WilliTourt/ESP32-Desktop-Drumkit-v0-Prototype/Hardware_PCB/Schematic/Piezo WaveHandler.png

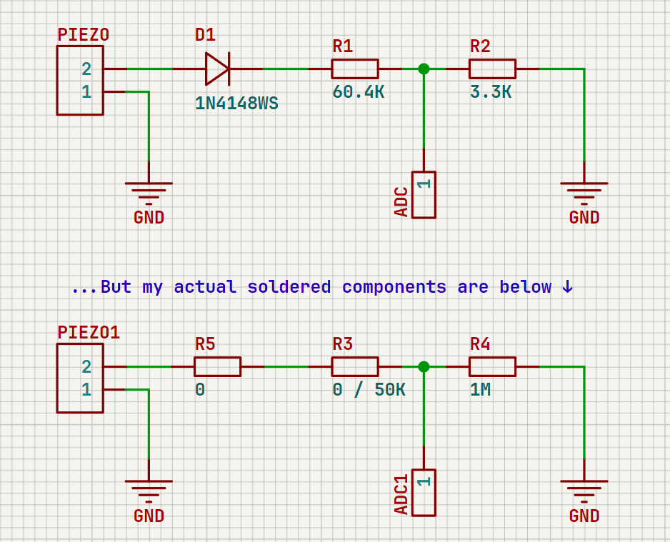
Hardware_PCB/Schematic/Piezo WaveHandler.png
