WilliTourt/ESP32-Desktop-Drumkit-v0-Prototype/Images of Drumkit/IMG_20250831_215929.jpg

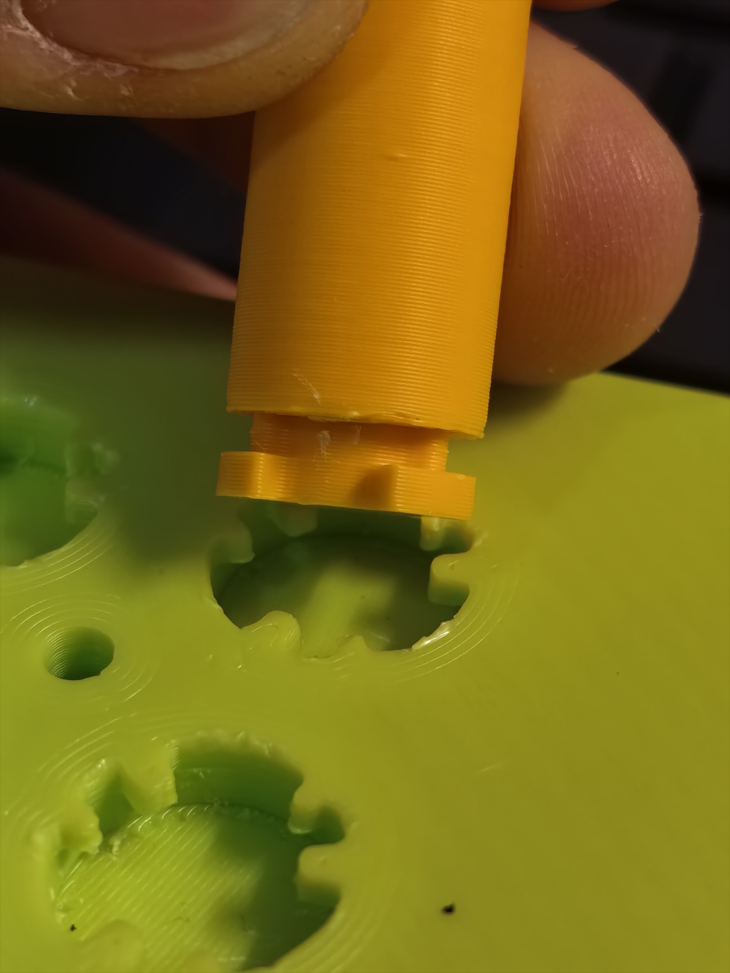
Images of Drumkit/IMG_20250831_215929.jpg
