WilliTourt/ESP32-Desktop-Drumkit-v0-Prototype/Images of Drumkit/IMG_20250901_182324.jpg

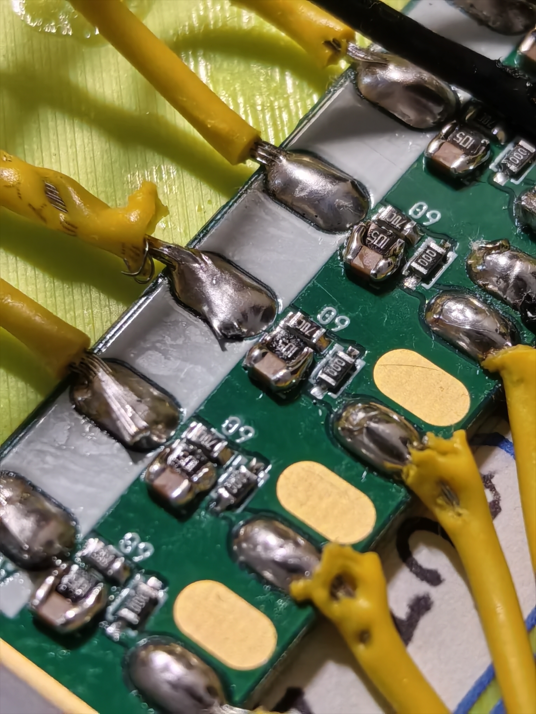
Images of Drumkit/IMG_20250901_182324.jpg
