WilliTourt/ESP32-Desktop-Drumkit-v0-Prototype/Images of Drumkit/IMG_20250902_012816.jpg

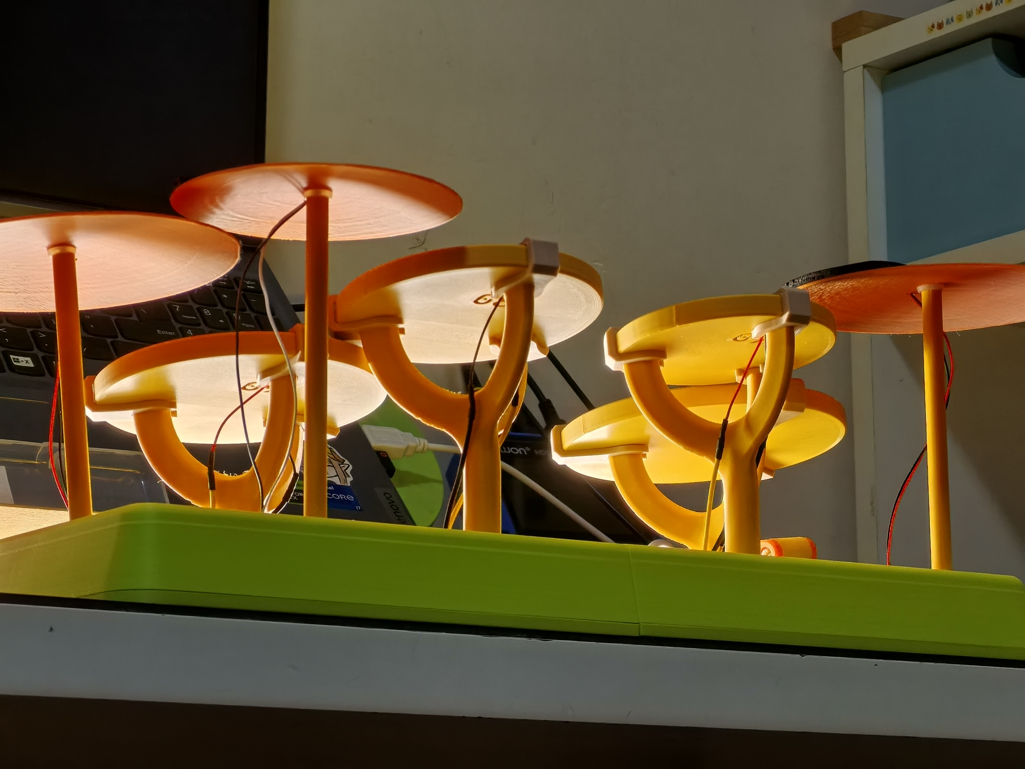
Images of Drumkit/IMG_20250902_012816.jpg
