WilliTourt/ESP32-Desktop-Drumkit-v0-Prototype/ESP32 Desktop Drumkit 3D Parts/STEP Files/Cymbal_9cm.STEP

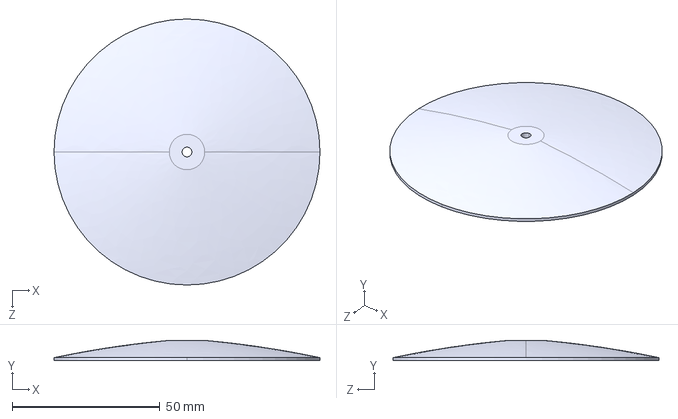
[picture p31: CAD file, 2025-09-04]
ESP32 Desktop Drumkit 3D Parts/STEP Files/Cymbal_9cm.STEP
90.0 x 6.85 x 90.0 mm
