WilliTourt/ESP32-Desktop-Drumkit-v0-Prototype/ESP32 Desktop Drumkit 3D Parts/STEP Files/CoverPlate_L.STEP

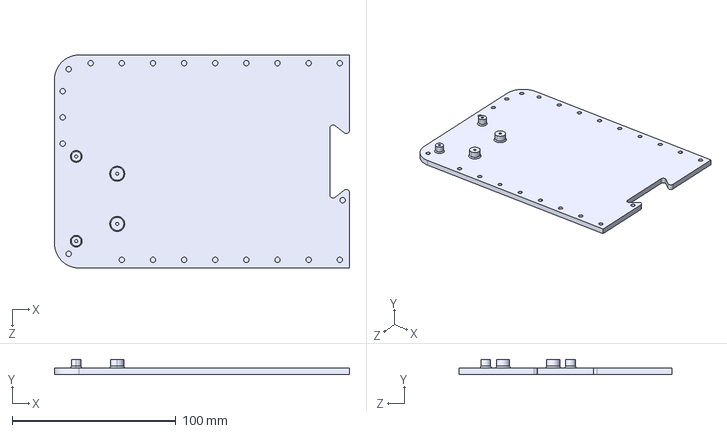
[picture p32: CAD file, 2025-09-04]
ESP32 Desktop Drumkit 3D Parts/STEP Files/CoverPlate_L.STEP
180.0 x 9.15 x 130.0 mm
