WilliTourt/ESP32-Desktop-Drumkit-v0-Prototype/ESP32 Desktop Drumkit 3D Parts/STEP Files/DrumPad_Leg+5.STEP

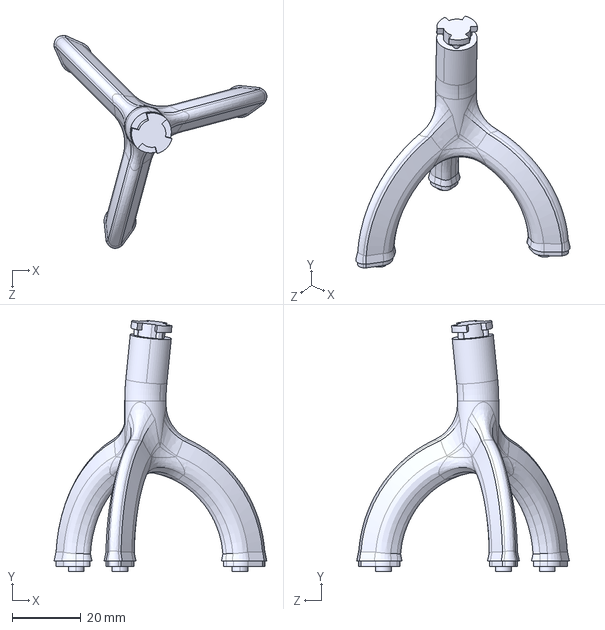
[picture p33: CAD file, 2025-09-04]
ESP32 Desktop Drumkit 3D Parts/STEP Files/DrumPad_Leg+5.STEP
61.8 x 72.9 x 61.8 mm
