WilliTourt/ESP32-Desktop-Drumkit-v0-Prototype/ESP32 Desktop Drumkit 3D Parts/STEP Files/Cymbal_11cm.STEP

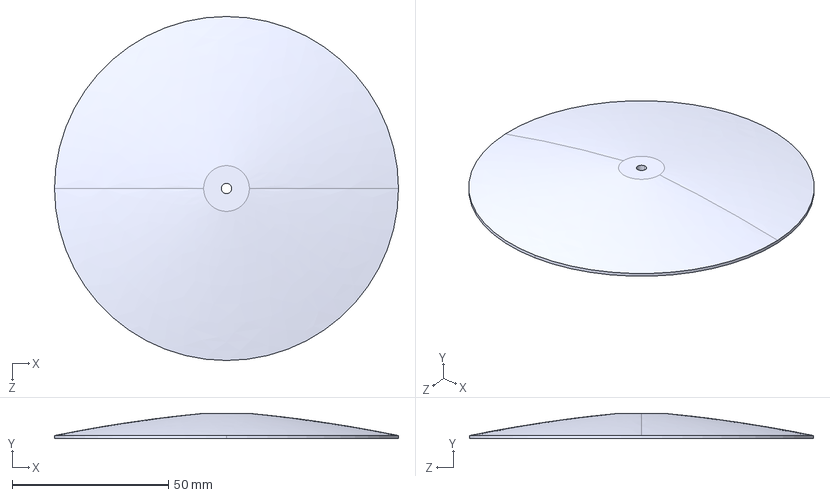
[picture p34: CAD file, 2025-09-04]
ESP32 Desktop Drumkit 3D Parts/STEP Files/Cymbal_11cm.STEP
110.0 x 8.10 x 110.0 mm
