WilliTourt/ESP32-Desktop-Drumkit-v0-Prototype/ESP32 Desktop Drumkit 3D Parts/STEP Files/Baseplate_L.STEP

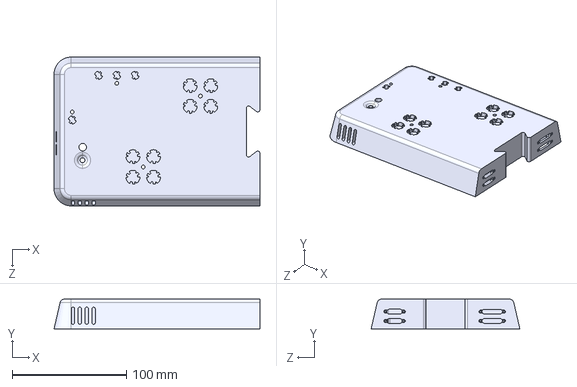
[picture p35: CAD file, 2025-09-04]
ESP32 Desktop Drumkit 3D Parts/STEP Files/Baseplate_L.STEP
180.0 x 26.0 x 130.0 mm
