WilliTourt/ESP32-Desktop-Drumkit-v0-Prototype/ESP32 Desktop Drumkit 3D Parts/STEP Files/DrumPad Fastener 09.STEP

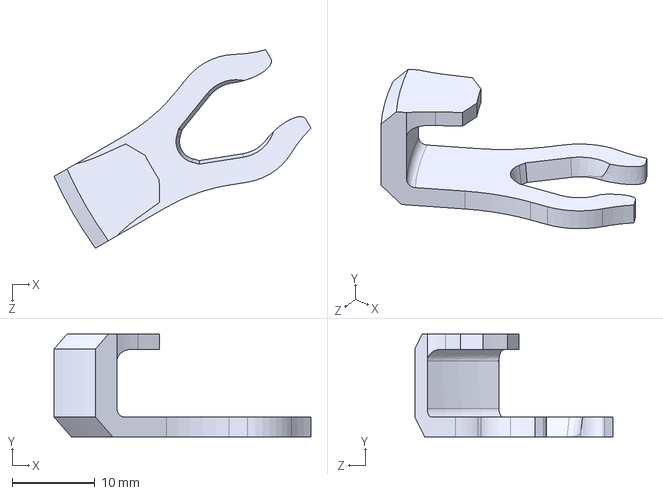
[picture p36: CAD file, 2025-09-04]
ESP32 Desktop Drumkit 3D Parts/STEP Files/DrumPad Fastener 09.STEP
31.0 x 12.4 x 23.9 mm
