WilliTourt/ESP32-Desktop-Drumkit-v0-Prototype/ESP32 Desktop Drumkit 3D Parts/STEP Files/Cymbal Stand.STEP

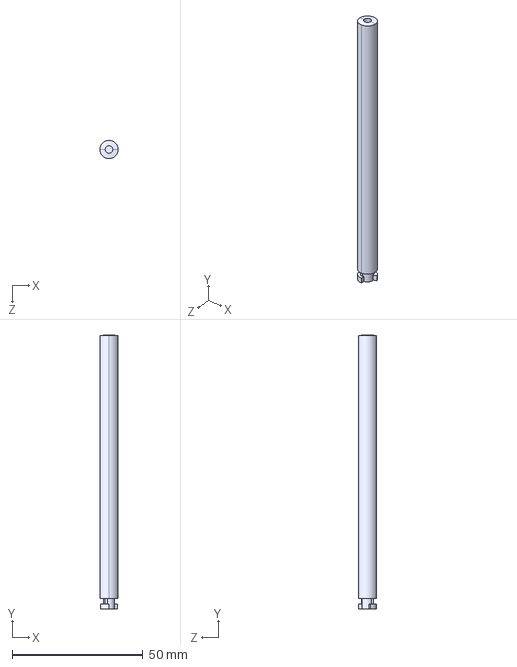
[picture p37: CAD file, 2025-09-04]
ESP32 Desktop Drumkit 3D Parts/STEP Files/Cymbal Stand.STEP
7.00 x 104.9 x 7.00 mm
