WilliTourt/ESP32-Desktop-Drumkit-v0-Prototype/ESP32 Desktop Drumkit 3D Parts/STEP Files/DrumPad_8cm.STEP

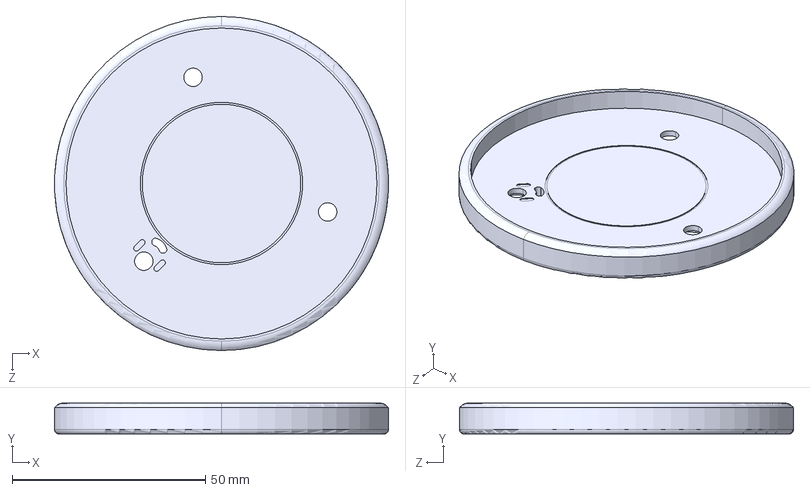
[picture p38: CAD file, 2025-09-04]
ESP32 Desktop Drumkit 3D Parts/STEP Files/DrumPad_8cm.STEP
86.4 x 8.00 x 86.4 mm
