WilliTourt/ESP32-Desktop-Drumkit-v0-Prototype/ESP32 Desktop Drumkit 3D Parts/STEP Files/CoverPlate_R.STEP

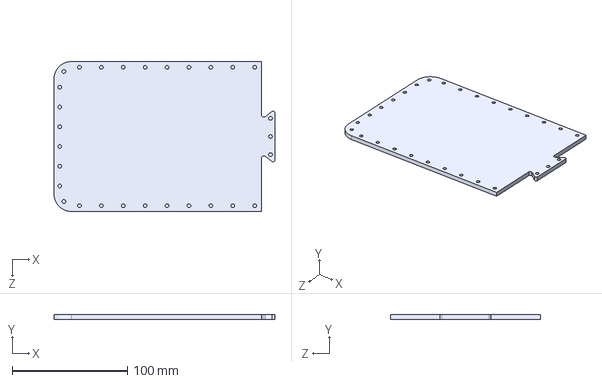
[picture p39: CAD file, 2025-09-04]
ESP32 Desktop Drumkit 3D Parts/STEP Files/CoverPlate_R.STEP
191.7 x 4.00 x 130.0 mm
