WilliTourt/ESP32-Desktop-Drumkit-v0-Prototype/ESP32 Desktop Drumkit 3D Parts/Solidworks/Fastener Chk.SLDASM

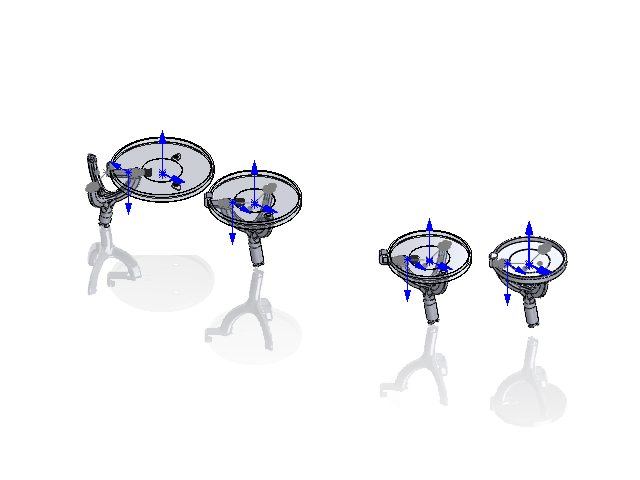
[picture p40: CAD file, 2025-09-04]
ESP32 Desktop Drumkit 3D Parts/Solidworks/Fastener Chk.SLDASM
DrumPad_7cm
DrumPad Fastener 07
DrumPad_Leg_Long x 3
DrumPad_8cm
DrumPad Fastener 09 x 2
DrumPad_10cm
DrumPad_9cm
DrumPad_Leg
DrumPad Fastener 10
