WilliTourt/ESP32-Desktop-Drumkit-v0-Prototype/ESP32 Desktop Drums/include/UsbMidi.h

#ifndef USBMIDI_H
#define USBMIDI_H

#include <Arduino.h>
#include <usb/usb_host.h>
#include <freertos/FreeRTOS.h>
#include <freertos/queue.h>
#include <atomic>

#define USB_MIDI_DEBUG 1
#define MIDI_OUT_QUEUE_SIZE 128

#define NUM_MIDI_IN_TRANSFERS 2
#define MAX_CLIENT_EVENT_MESSAGES 5
#define USB_EVENT_POLL_TICKS 1
#define USB_AUDIO_SUBCLASS_MIDI_STREAMING 3

#if USB_MIDI_DEBUG
#define USB_MIDI_LOG(format, ...)                 \
    do {                                          \
        if (this->_debugSerial) {                 \
            this->_debugSerial->printf(format, ##__VA_ARGS__); \
        }                                         \
    } while (0)
#else
#define USB_MIDI_LOG(format, ...) \
    do {                          \
    } while (0)
#endif

enum class MidiCin : uint8_t {
    NOTE_OFF = 0x08,
    NOTE_ON = 0x09,
    CONTROL_CHANGE = 0x0B,
    PROGRAM_CHANGE = 0x0C,
};

class UsbMidi {
public:
    using MidiMessageCallback = void (*)(const uint8_t (&)[4]);
    

    UsbMidi(Stream* debugSerial = nullptr);
    ~UsbMidi();

    void begin();
    void end();
    void update();

    void onMidiMessage(MidiMessageCallback callback);

    bool sendMidiMessage(const uint8_t* message, uint8_t size = 4);
    bool noteOn(uint8_t channel, uint8_t note, uint8_t velocity);
    bool noteOff(uint8_t channel, uint8_t note, uint8_t velocity);
    bool controlChange(uint8_t channel, uint8_t controller, uint8_t value);
    bool programChange(uint8_t channel, uint8_t program);

    size_t getQueueAvailableSize() const;

    void onDeviceConnected(void (*callback)());
    void onDeviceDisconnected(void (*callback)());

private:
    static void _clientEventCallback(const usb_host_client_event_msg_t* eventMsg, void* arg);
    static void _midiTransferCallback(usb_transfer_t* transfer);

    void _handleClientEvent(const usb_host_client_event_msg_t* eventMsg);
    void _handleMidiTransfer(usb_transfer_t* transfer);
    void _parseConfigDescriptor(const usb_config_desc_t* configDesc);
    void _findAndClaimMidiInterface(const usb_intf_desc_t* intf);
    void _setupMidiEndpoints(const usb_ep_desc_t* endpoint);
    void _setupMidiInEndpoint(const usb_ep_desc_t* endpoint);
    void _setupMidiOutEndpoint(const usb_ep_desc_t* endpoint);
    void _releaseDeviceResources();
    void _processMidiOutQueue();

    usb_host_client_handle_t _clientHandle;
    usb_device_handle_t _deviceHandle;
    usb_transfer_t* _midiOutTransfer;
    usb_transfer_t* _midiInTransfers[NUM_MIDI_IN_TRANSFERS];
    QueueHandle_t _midiOutQueue;
    uint8_t _midiInterfaceNumber;
    bool _isMidiInterfaceFound;
    bool _areEndpointsReady;
    std::atomic<bool> _isMidiOutBusy; 
    MidiMessageCallback _midiMessageCallback;
    void (*_deviceConnectedCallback)();
    void (*_deviceDisconnectedCallback)();
    Stream* _debugSerial;
};

#endif // USBMIDI_H
